kikithegecko/master_thesis/documentation/slides final/01.JPG

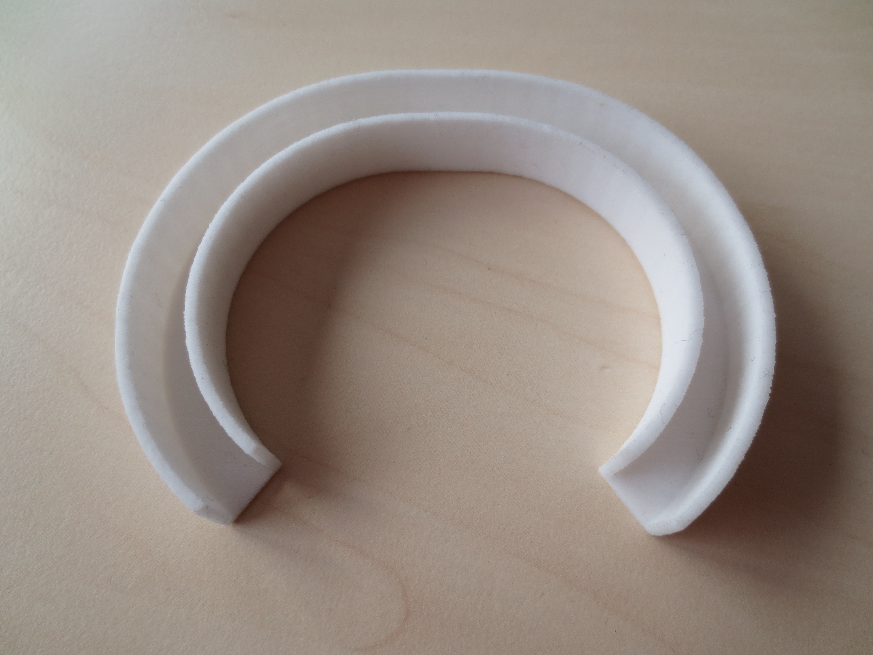
documentation/slides final/01.JPG
