kikithegecko/master_thesis/documentation/slides final/02.JPG

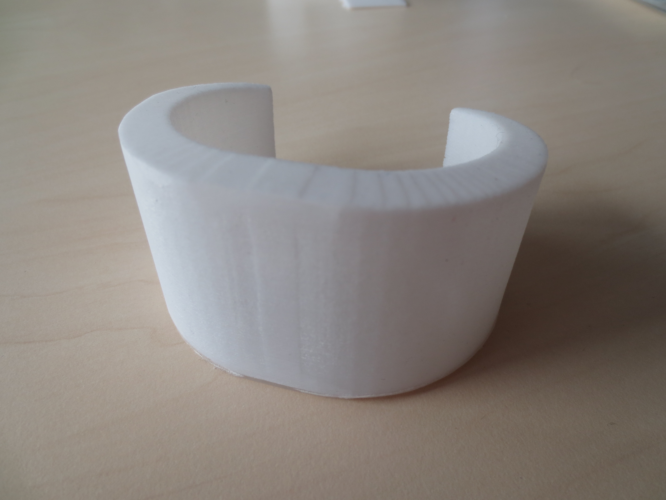
documentation/slides final/02.JPG
