kikithegecko/master_thesis/documentation/slides final/03.JPG

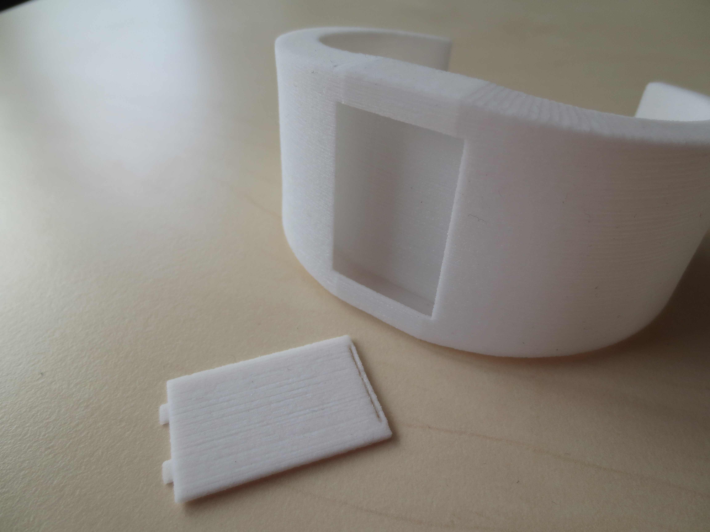
documentation/slides final/03.JPG
