kikithegecko/master_thesis/documentation/slides final/04.jpg

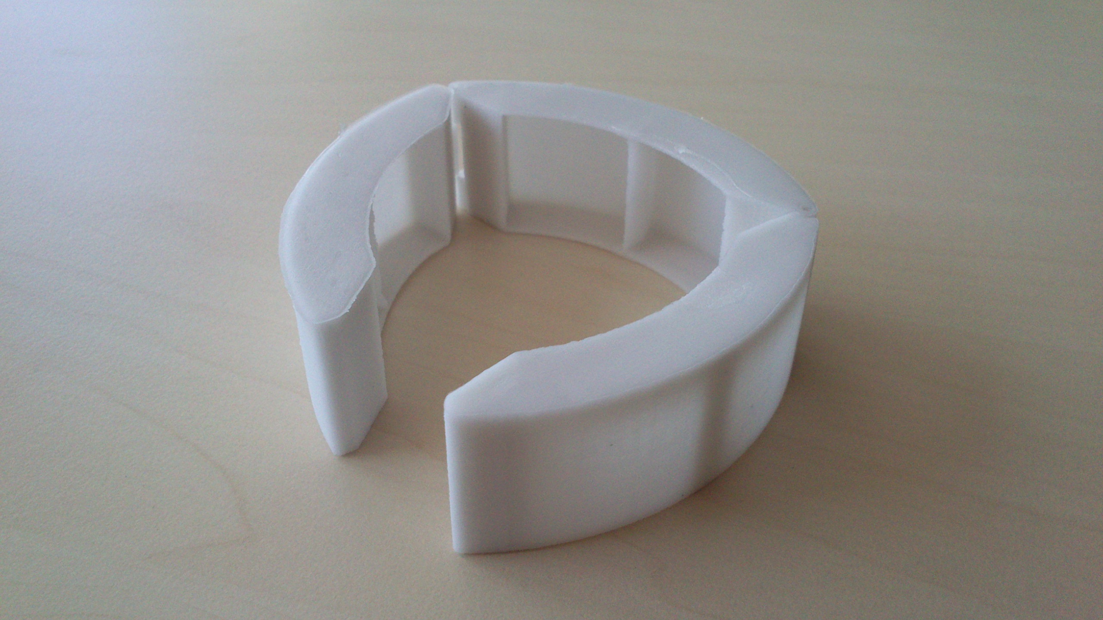
documentation/slides final/04.jpg
