kikithegecko/master_thesis/documentation/slides final/05.JPG

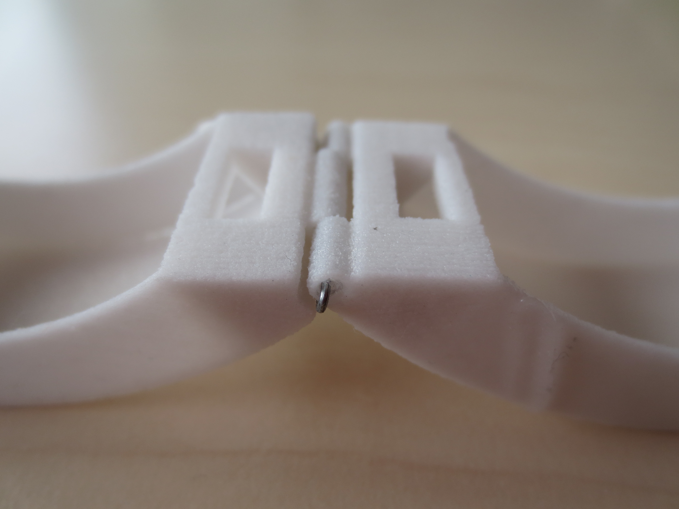
documentation/slides final/05.JPG
