kikithegecko/master_thesis/documentation/slides final/07.JPG

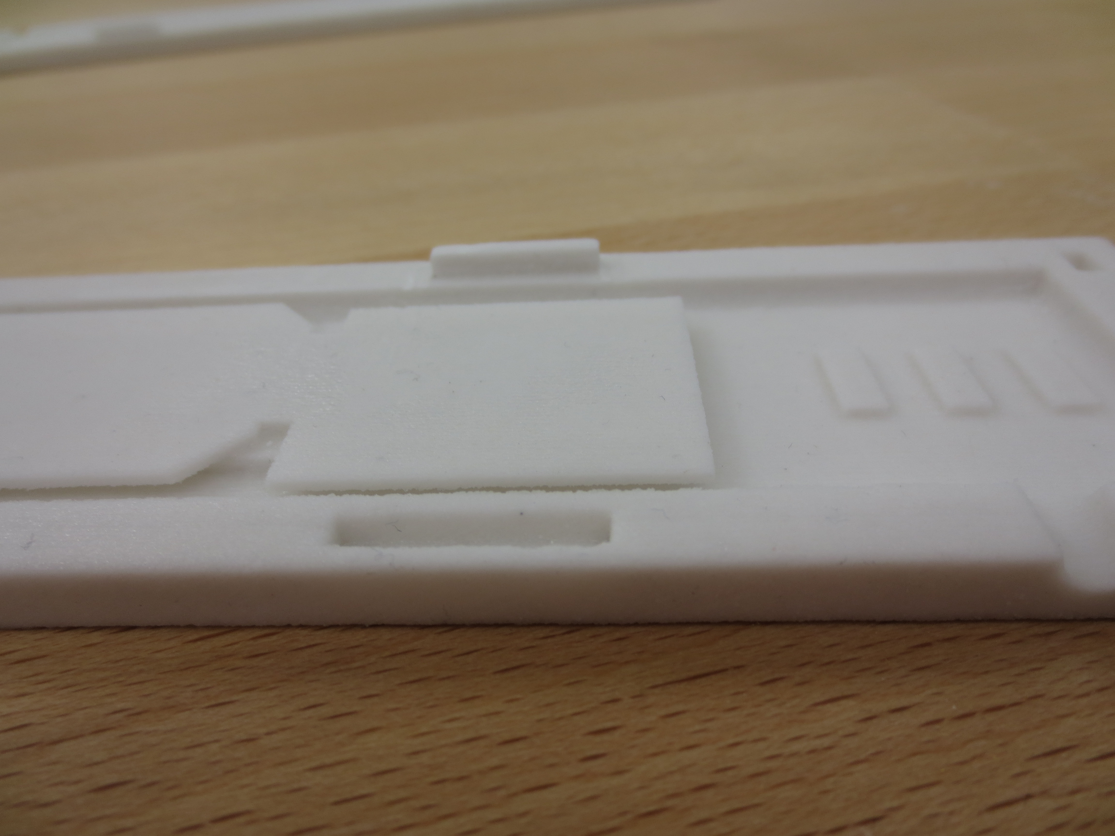
documentation/slides final/07.JPG
