kikithegecko/master_thesis/documentation/slides final/08.JPG

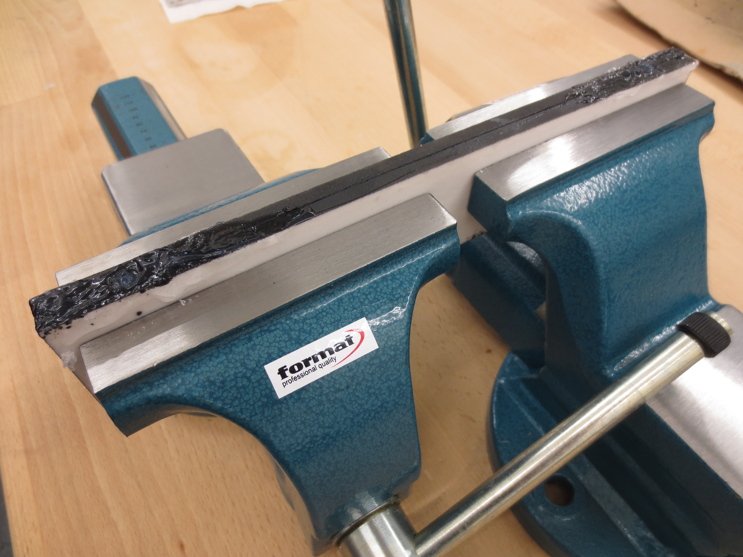
documentation/slides final/08.JPG
