kikithegecko/master_thesis/documentation/slides final/10.JPG

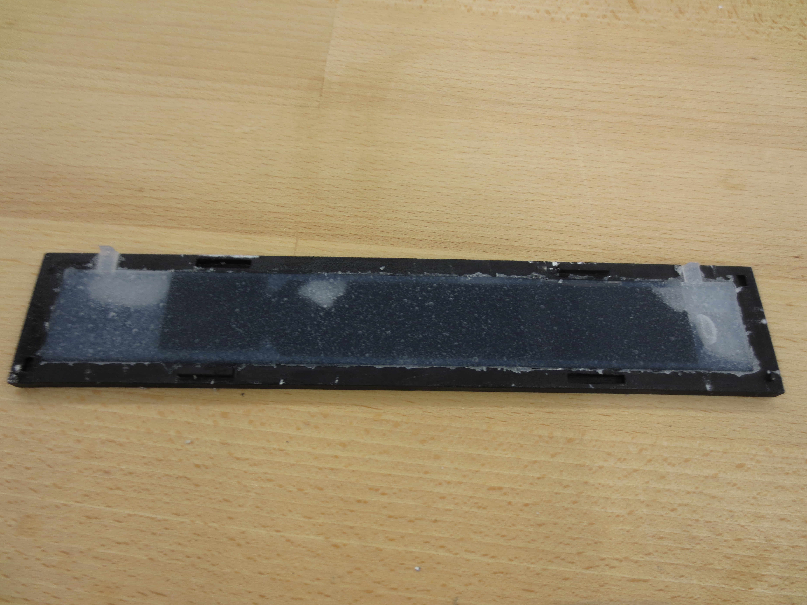
documentation/slides final/10.JPG
