kikithegecko/master_thesis/documentation/slides final/13.JPG

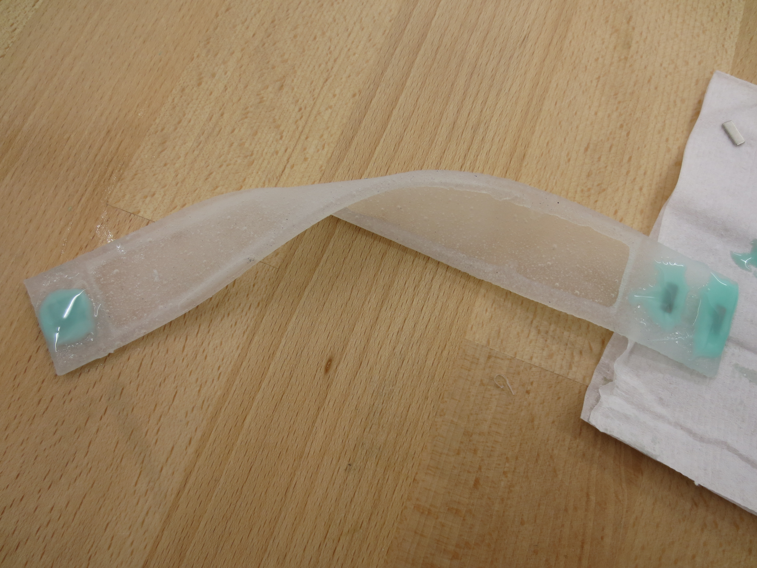
documentation/slides final/13.JPG
