kikithegecko/master_thesis/documentation/slides final/14.JPG

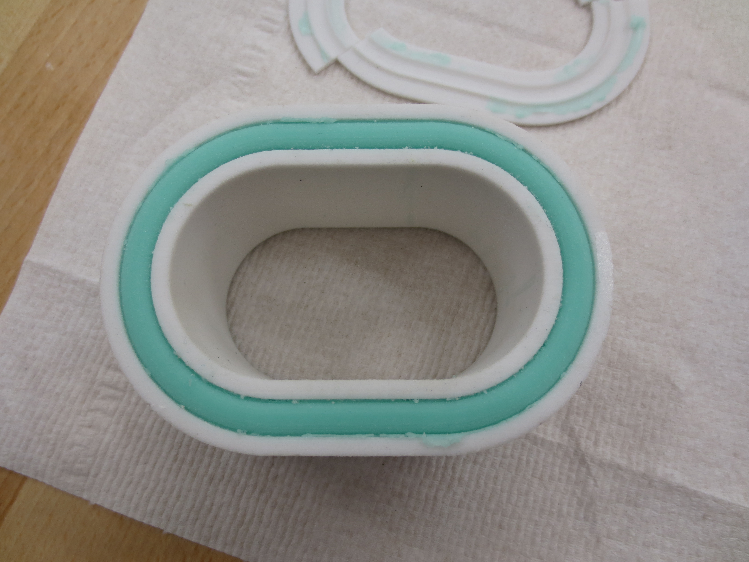
documentation/slides final/14.JPG
