kikithegecko/master_thesis/documentation/slides final/15.JPG

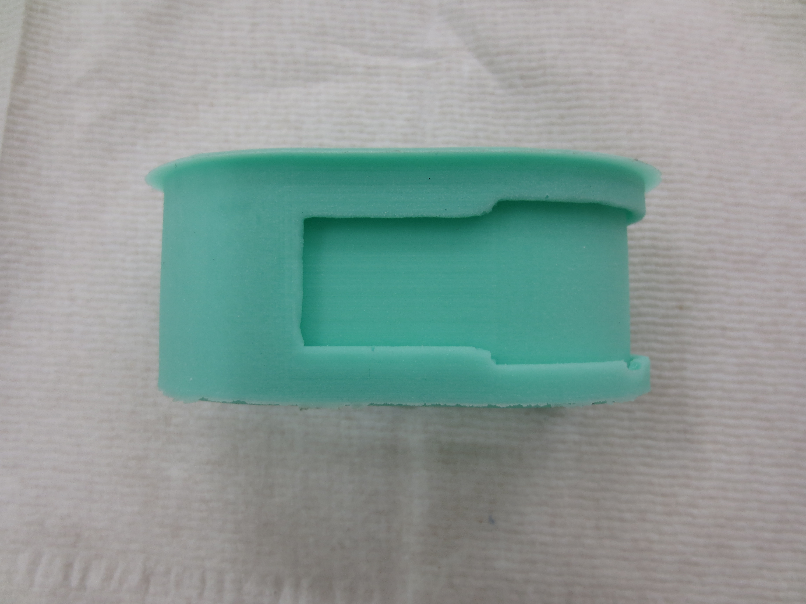
documentation/slides final/15.JPG
