kikithegecko/master_thesis/documentation/slides final/16.JPG

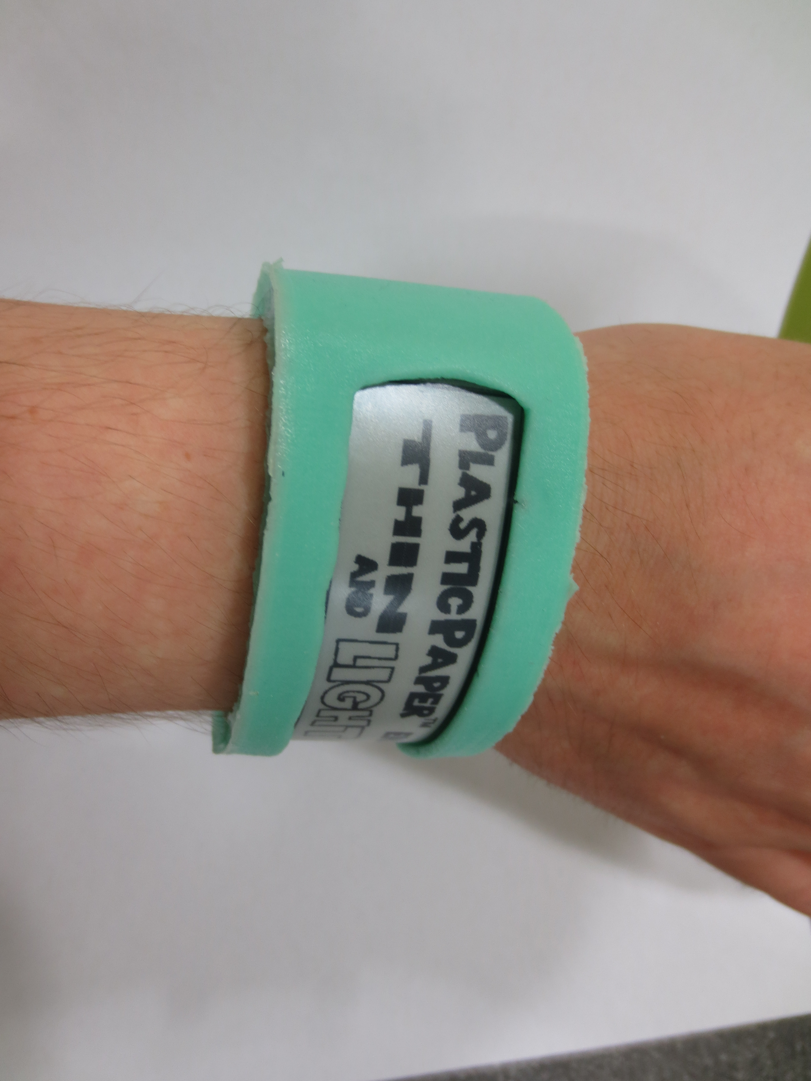
documentation/slides final/16.JPG
