kikithegecko/master_thesis/documentation/slides final/17.JPG

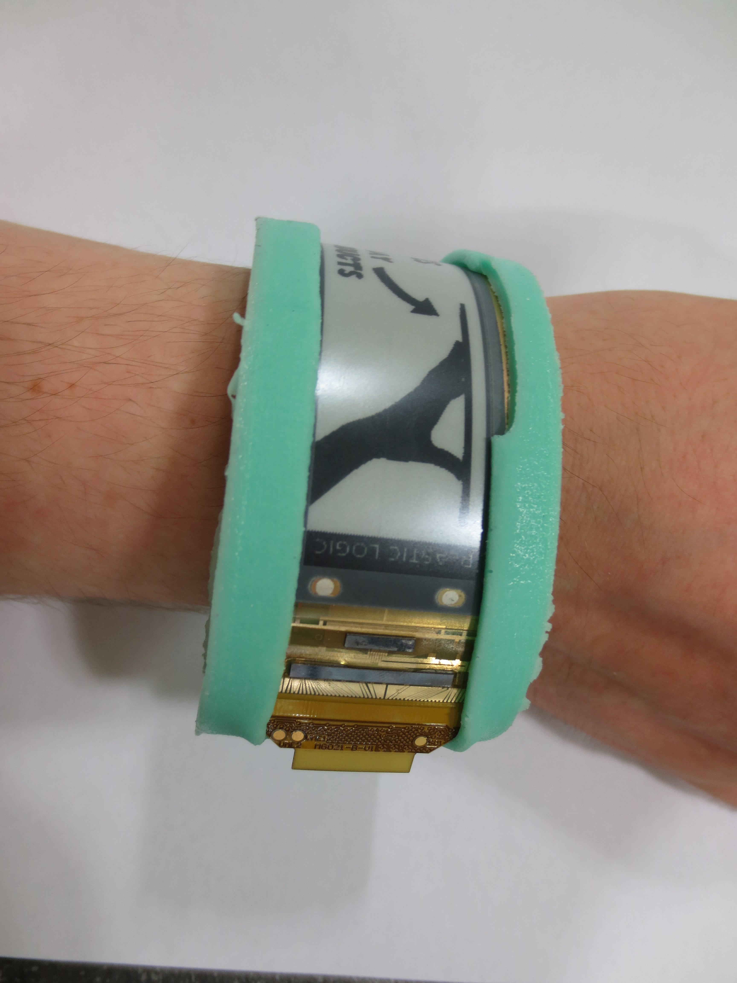
documentation/slides final/17.JPG
