kikithegecko/master_thesis/documentation/slides kick-off/finished.png

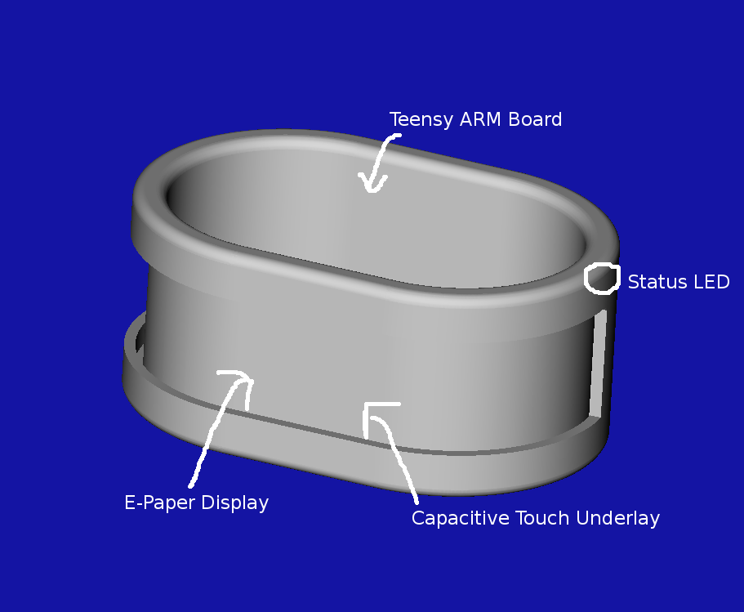
documentation/slides kick-off/finished.png
