kikithegecko/master_thesis/documentation/slides kick-off/IMG_0398.JPG

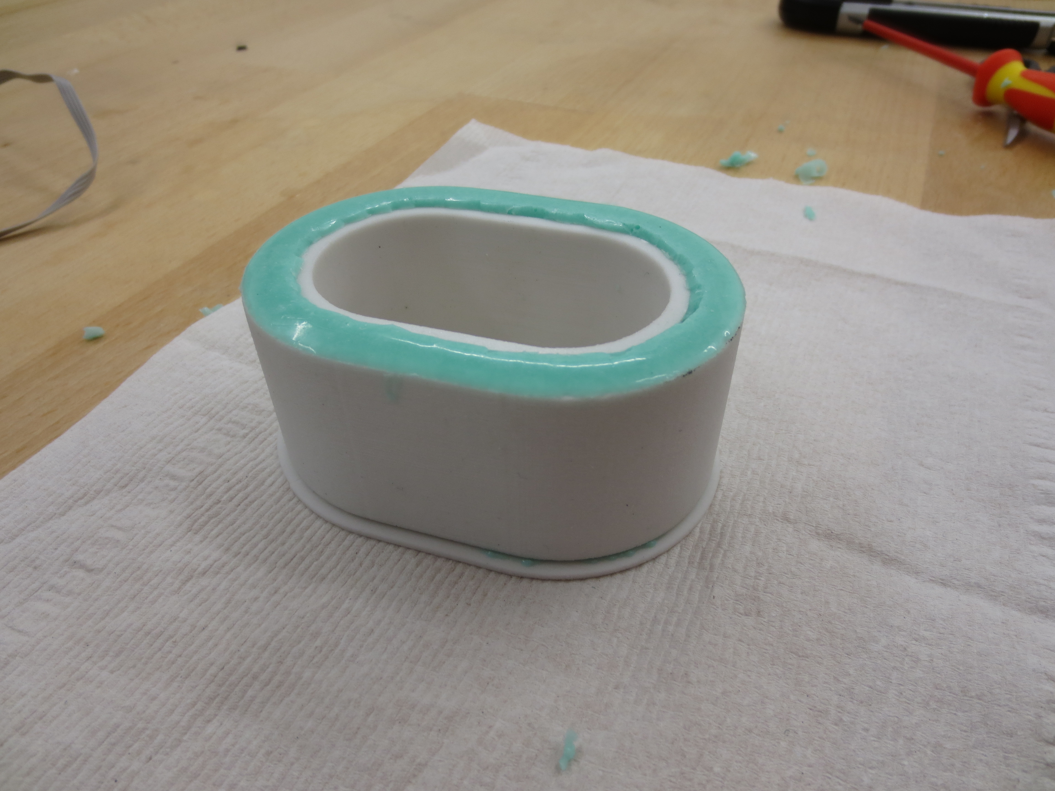
documentation/slides kick-off/IMG_0398.JPG
