kikithegecko/master_thesis/documentation/slides kick-off/IMG_0413.JPG

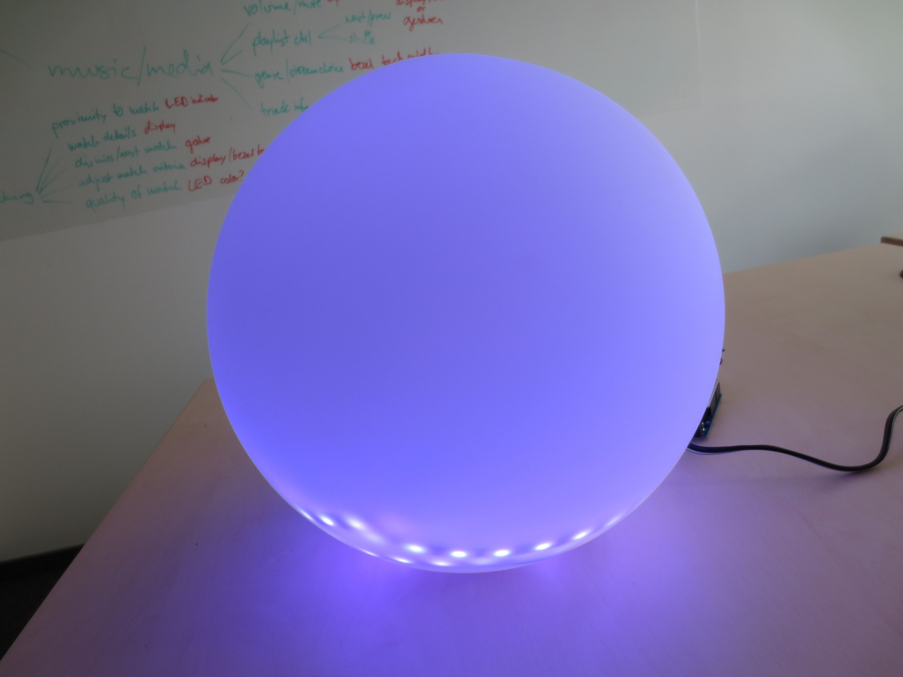
documentation/slides kick-off/IMG_0413.JPG
