kikithegecko/master_thesis/documentation/slides kick-off/IMG_0414.JPG

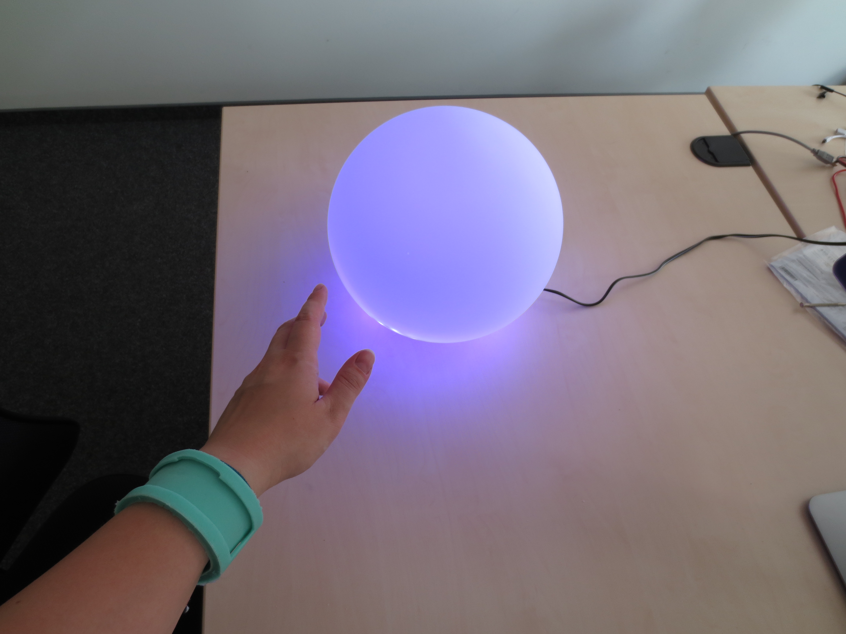
documentation/slides kick-off/IMG_0414.JPG
