kikithegecko/master_thesis/documentation/slides kick-off/IMG_0415.JPG

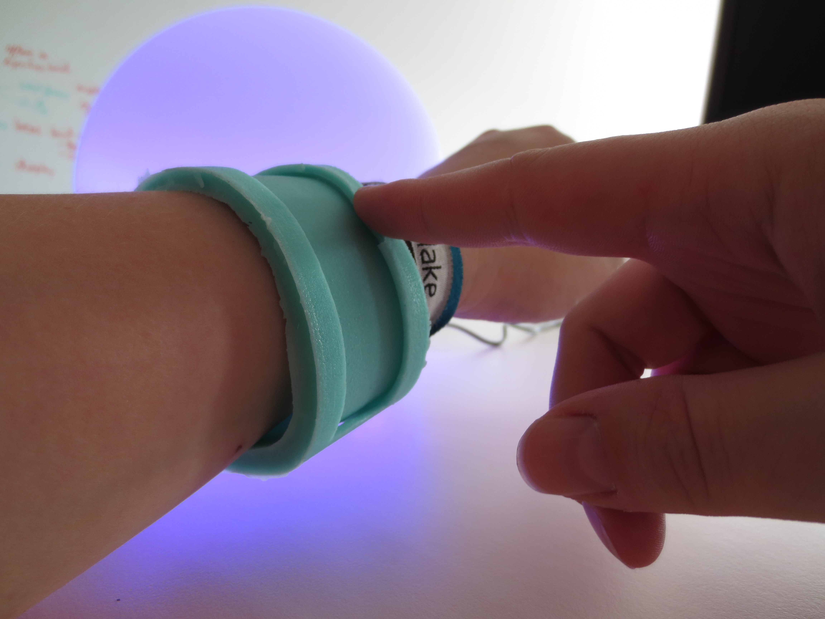
documentation/slides kick-off/IMG_0415.JPG
