kikithegecko/master_thesis/documentation/slides kick-off/IMG_0416.JPG

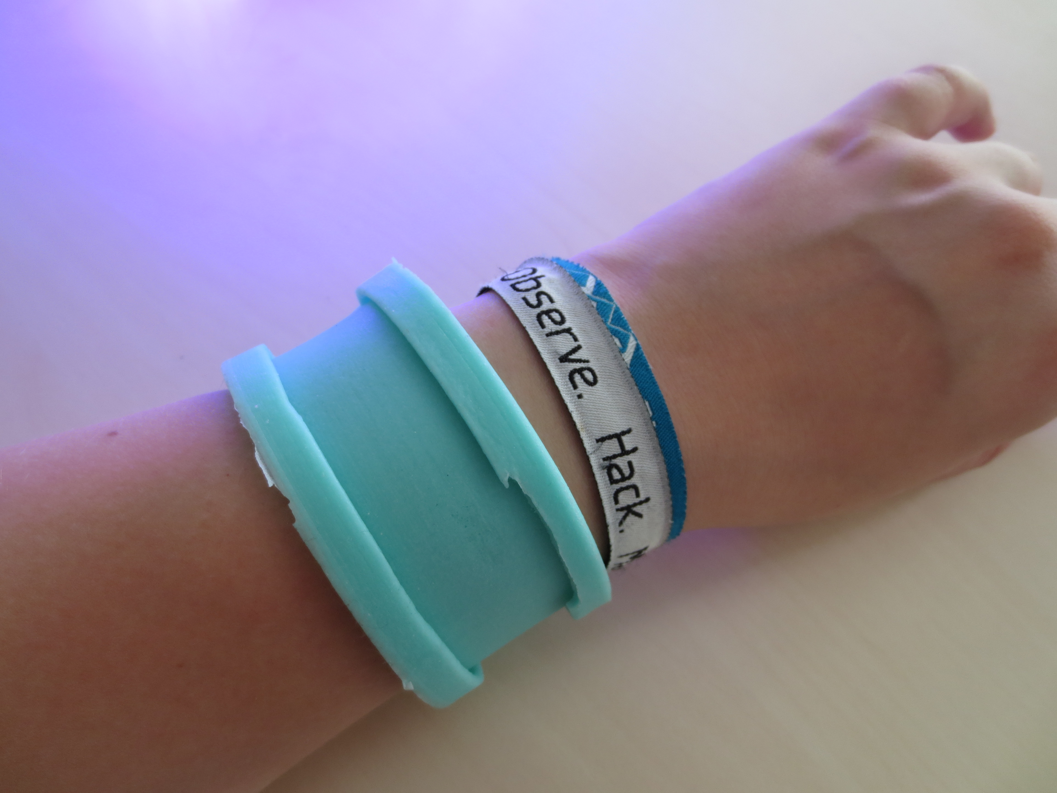
documentation/slides kick-off/IMG_0416.JPG
