kikithegecko/master_thesis/prints/06_mold2_inner.FCStd

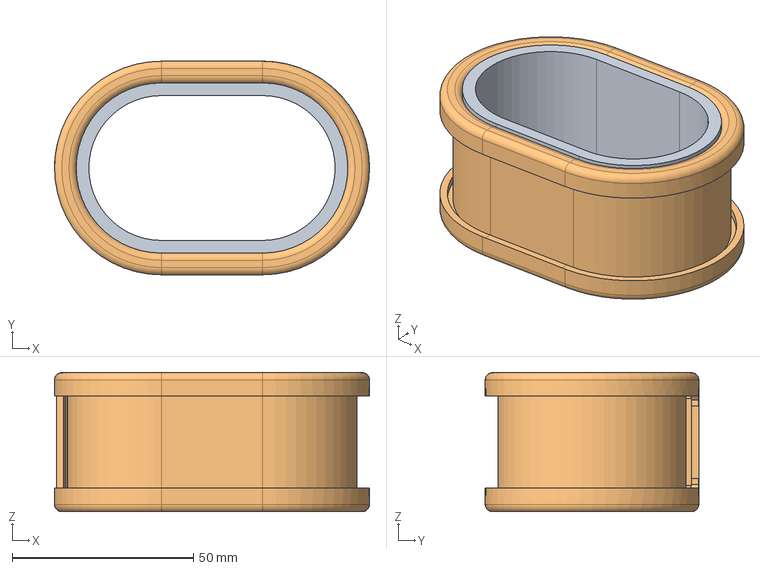
[picture p83: CAD file, 2014-07-16]
prints/06_mold2_inner.FCStd
87.0 x 59.0 x 38.5 mm
inner
