kikithegecko/master_thesis/prints/06_mold2.FCStd

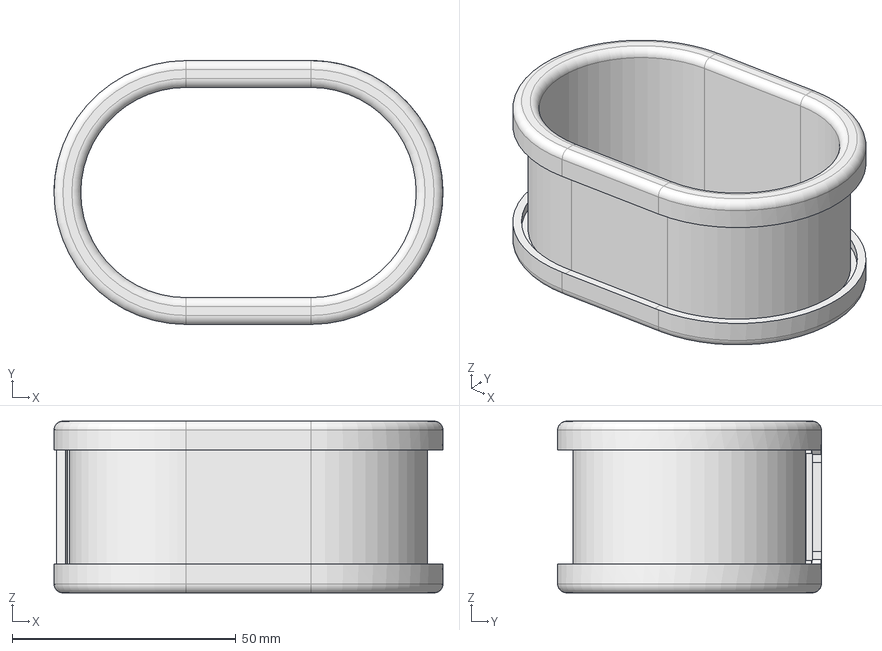
[picture p84: CAD file, 2014-07-16]
prints/06_mold2.FCStd
87.0 x 59.0 x 38.4 mm
