kikithegecko/master_thesis/prints/06_mold2_base.FCStd

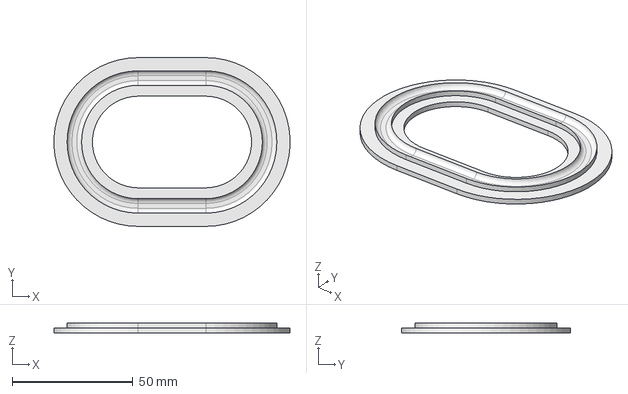
[picture p85: CAD file, 2014-07-16]
prints/06_mold2_base.FCStd
97.9 x 70.0 x 4.00 mm
