kikithegecko/master_thesis/prints/06_mold2_outer.FCStd

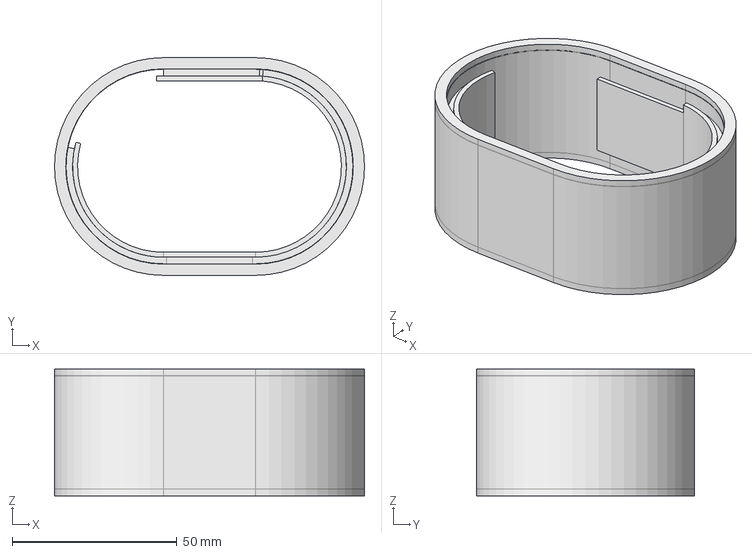
[picture p86: CAD file, 2014-07-16]
prints/06_mold2_outer.FCStd
94.0 x 66.0 x 38.4 mm
