kikithegecko/master_thesis/prints/06_mold2_finished_product.FCStd

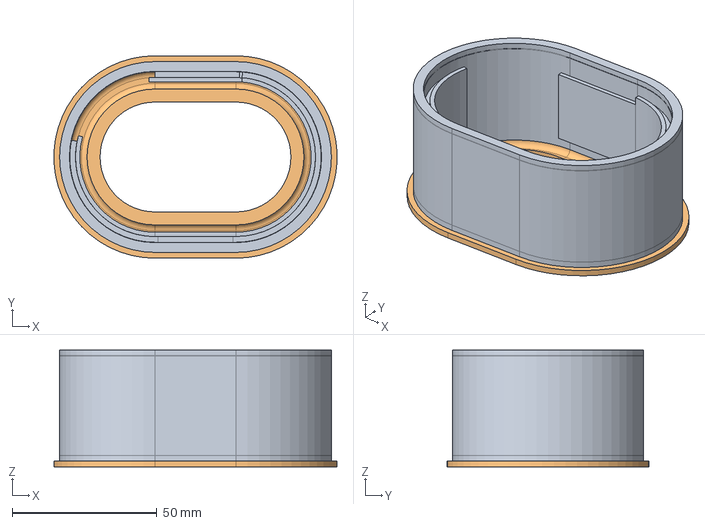
[picture p87: CAD file, 2014-07-16]
prints/06_mold2_finished_product.FCStd
97.9 x 70.0 x 40.4 mm
outer
base
