kikithegecko/master_thesis/prints/05_silicone_bracelet_moldable.FCStd

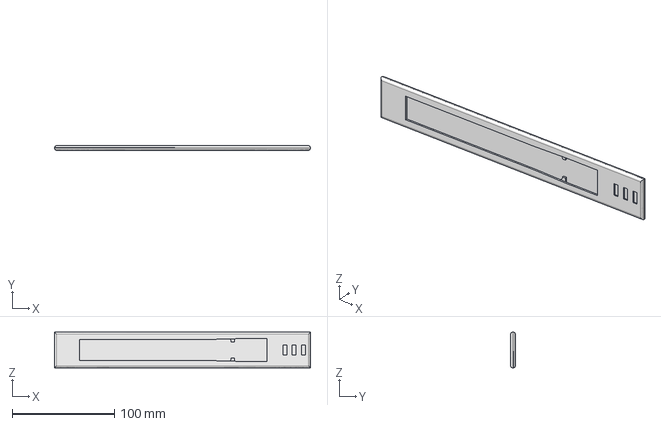
[picture p88: CAD file, 2014-07-10]
prints/05_silicone_bracelet_moldable.FCStd
250.0 x 4.50 x 35.0 mm
