kikithegecko/master_thesis/prints/05_silicone_bracelet_mold.FCStd

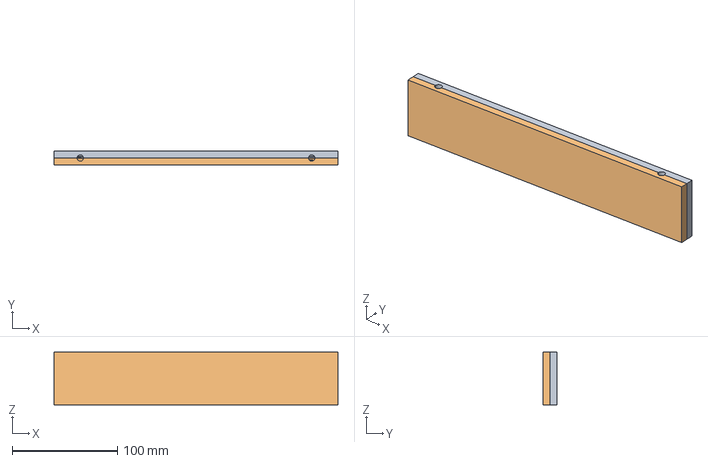
[picture p89: CAD file, 2014-07-10]
prints/05_silicone_bracelet_mold.FCStd
270.0 x 13.0 x 50.0 mm
