kikithegecko/master_thesis/prints/02a_confortable_cuff_improved.FCStd

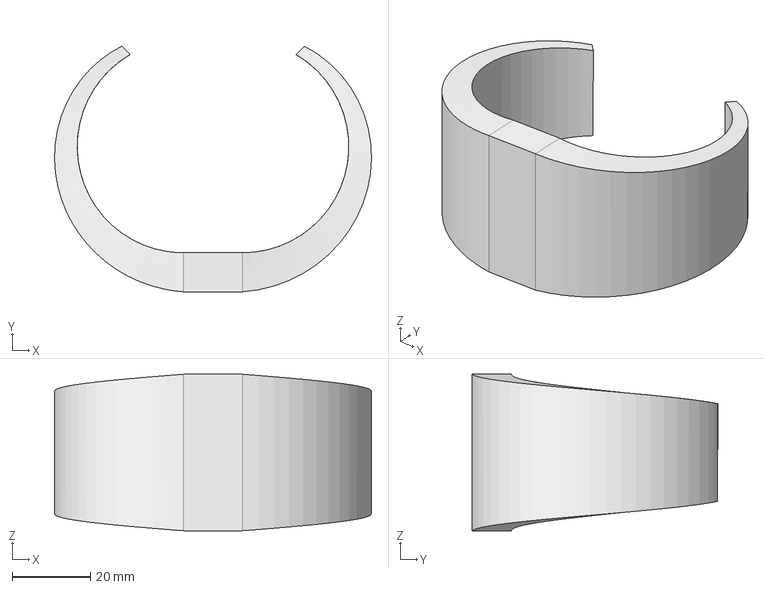
[picture p90: CAD file, 2014-06-16]
prints/02a_confortable_cuff_improved.FCStd
81.0 x 62.8 x 40.0 mm
