kikithegecko/master_thesis/prints/02a_lid.FCStd

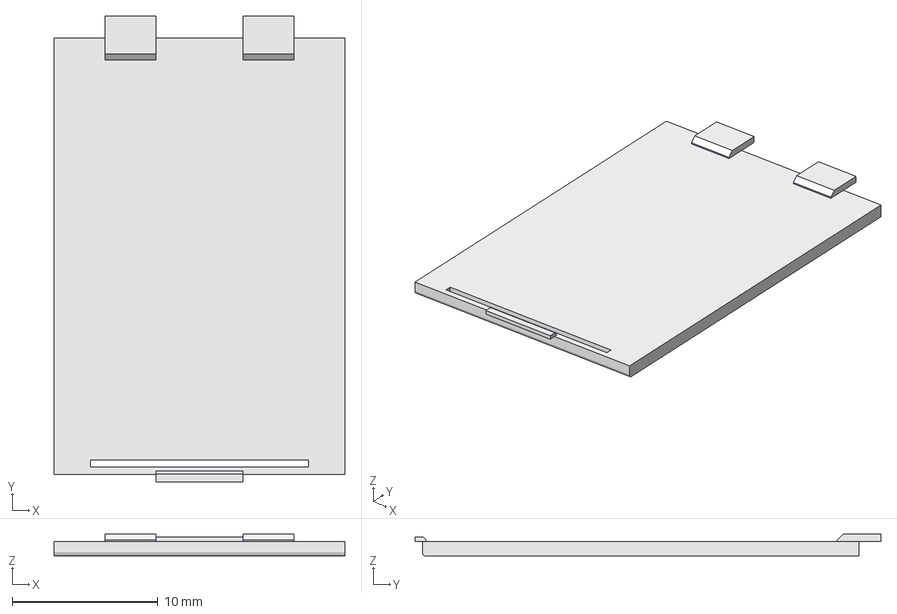
[picture p91: CAD file, 2014-06-16]
prints/02a_lid.FCStd
20.0 x 32.0 x 1.50 mm
