kikithegecko/master_thesis/prints/04b_tri_part_end.FCStd

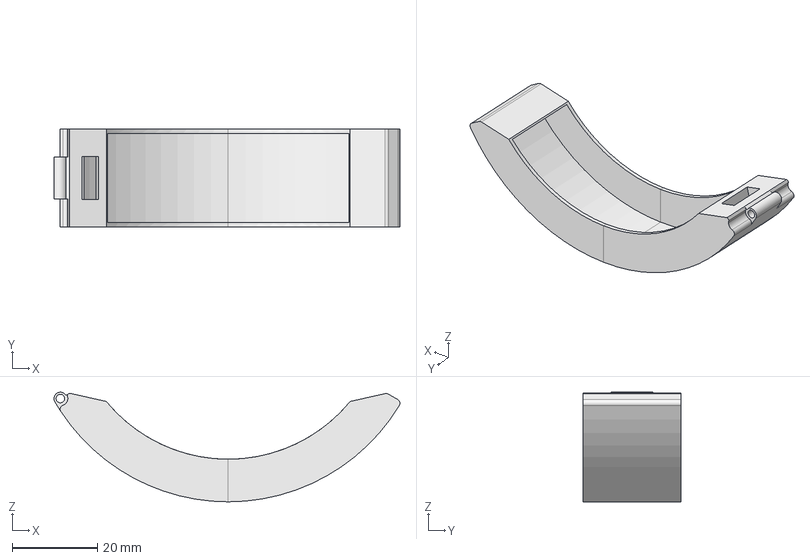
[picture p92: CAD file, 2014-05-23]
prints/04b_tri_part_end.FCStd
81.2 x 23.0 x 25.7 mm
