kikithegecko/master_thesis/prints/04b_tri_part_middle.FCStd

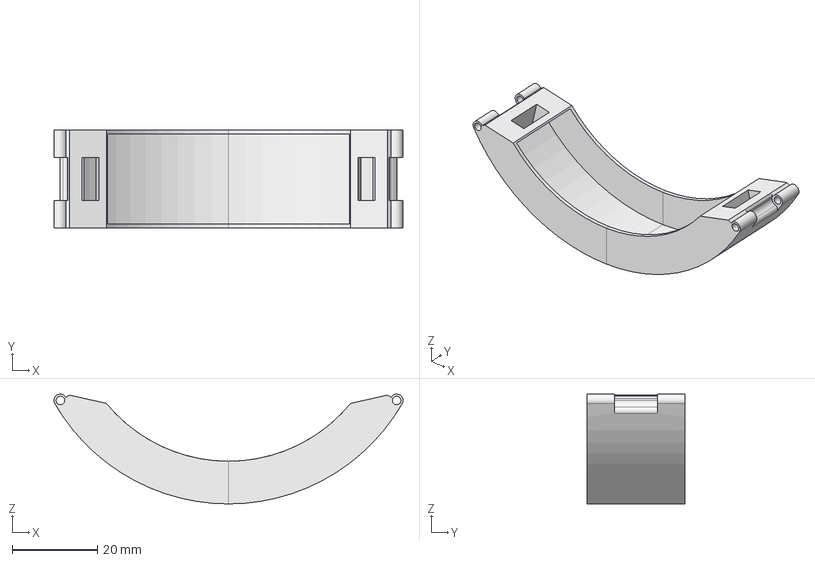
[picture p93: CAD file, 2014-05-23]
prints/04b_tri_part_middle.FCStd
81.8 x 23.0 x 25.7 mm
