kikithegecko/master_thesis/prints/04a_tri_part_middle.FCStd

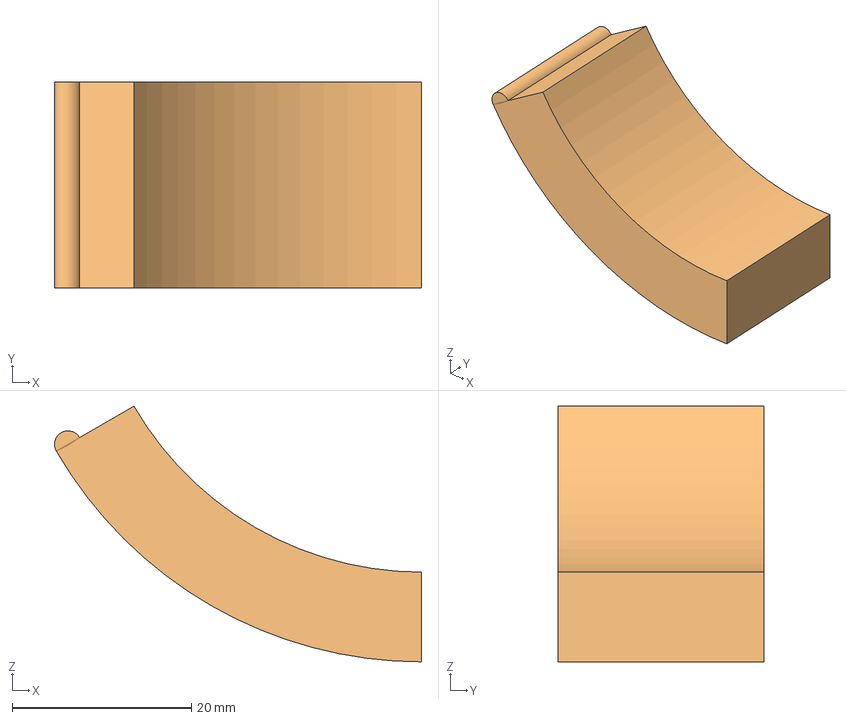
[picture p94: CAD file, 2014-05-23]
prints/04a_tri_part_middle.FCStd
40.9 x 23.0 x 28.5 mm
hinge cut
hinge pad
Sweep profile
