kikithegecko/master_thesis/prints/04_tri_part_end.FCStd

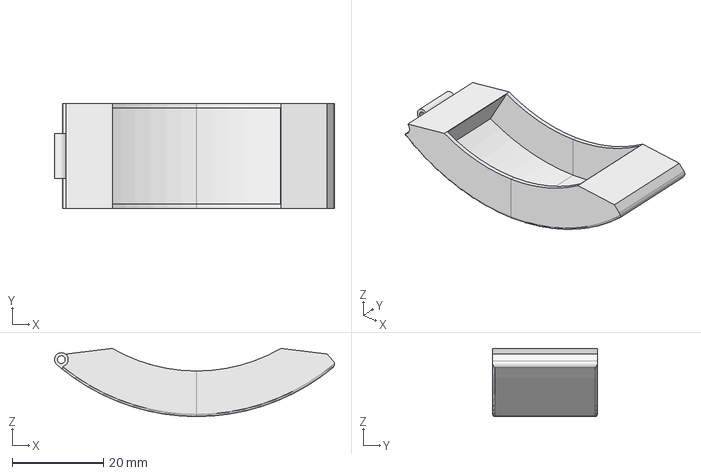
[picture p95: CAD file, 2014-05-20]
prints/04_tri_part_end.FCStd
61.4 x 23.0 x 15.0 mm
