kikithegecko/master_thesis/prints/04_tri_part_middle.FCStd

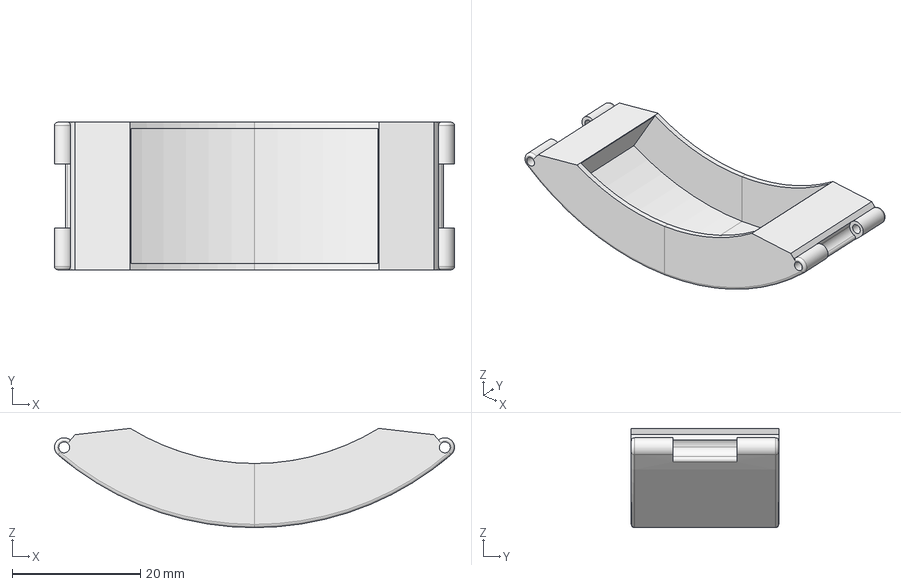
[picture p96: CAD file, 2014-05-20]
prints/04_tri_part_middle.FCStd
62.4 x 23.0 x 15.5 mm
