kikithegecko/master_thesis/prints/03_amico_side.stl

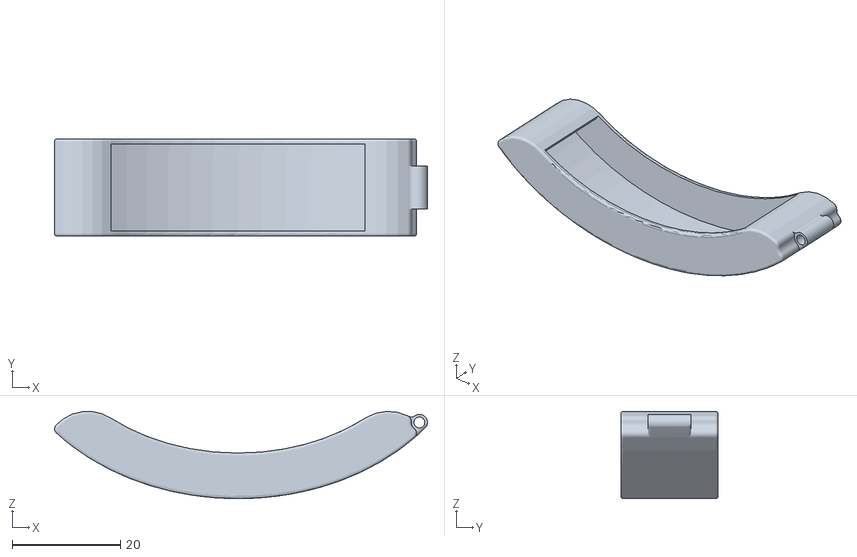
[picture p97: CAD file, 2014-05-20]
prints/03_amico_side.stl
68.9 x 18.0 x 16.1
