kikithegecko/master_thesis/prints/03_amico_bracelet.stl

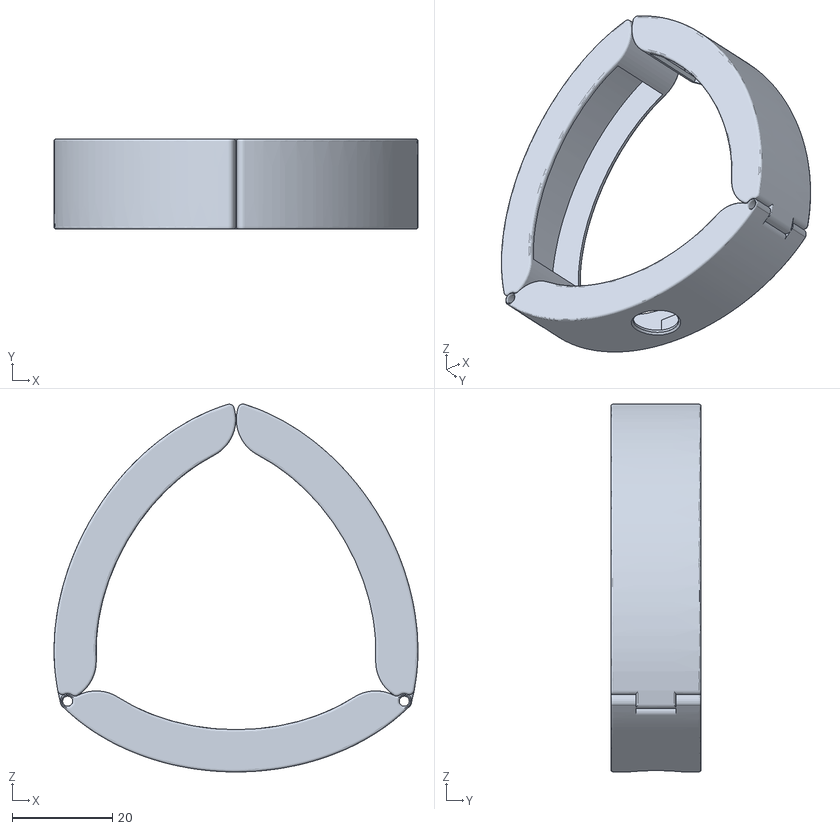
[picture p98: CAD file, 2014-05-20]
prints/03_amico_bracelet.stl
72.4 x 18.0 x 73.2
