kikithegecko/master_thesis/prints/03_amico_front.stl

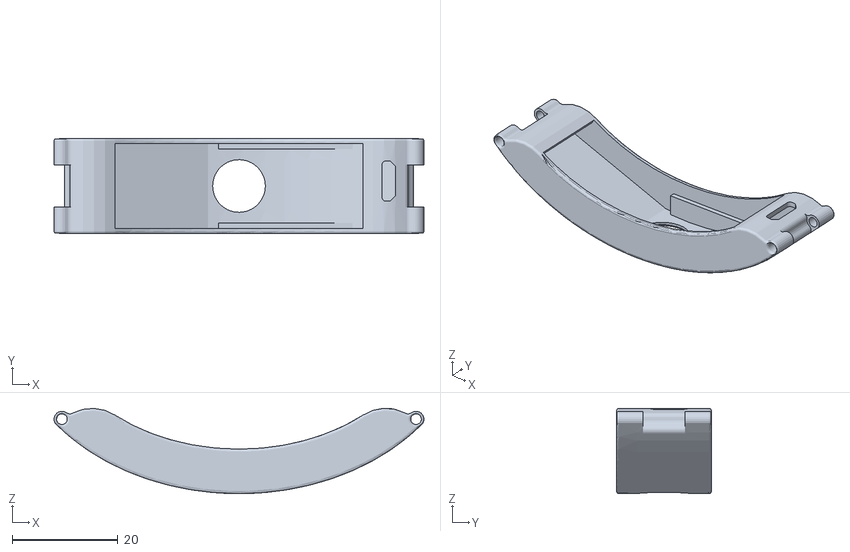
[picture p99: CAD file, 2014-05-20]
prints/03_amico_front.stl
70.0 x 18.0 x 16.1
