kikithegecko/master_thesis/prints/02_comfortable_cuff.FCStd

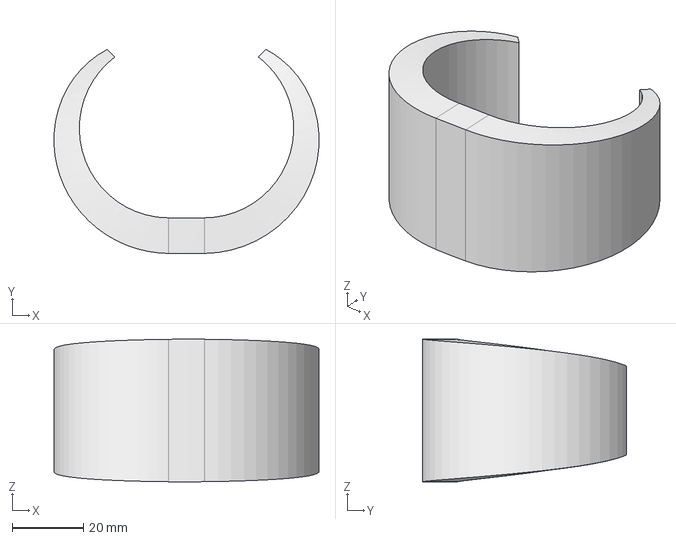
[picture p100: CAD file, 2014-05-20]
prints/02_comfortable_cuff.FCStd
74.4 x 57.3 x 40.1 mm
