kikithegecko/master_thesis/prints/01_simple_cuff.FCStd

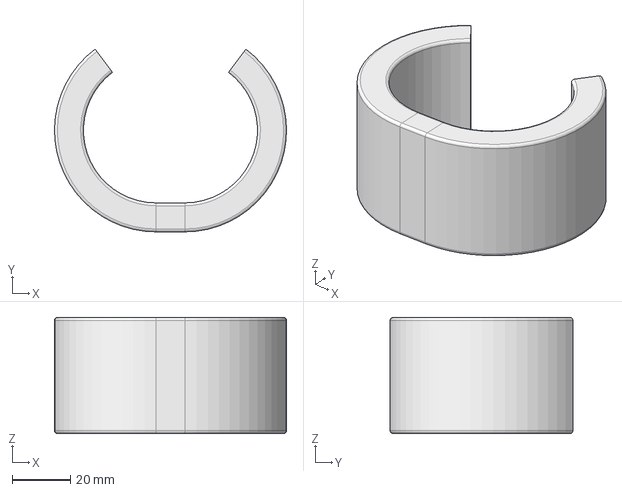
[picture p101: CAD file, 2014-05-20]
prints/01_simple_cuff.FCStd
80.0 x 63.0 x 40.0 mm
