kikithegecko/master_thesis/prints/01_simple_cuff_no_fillets.stl

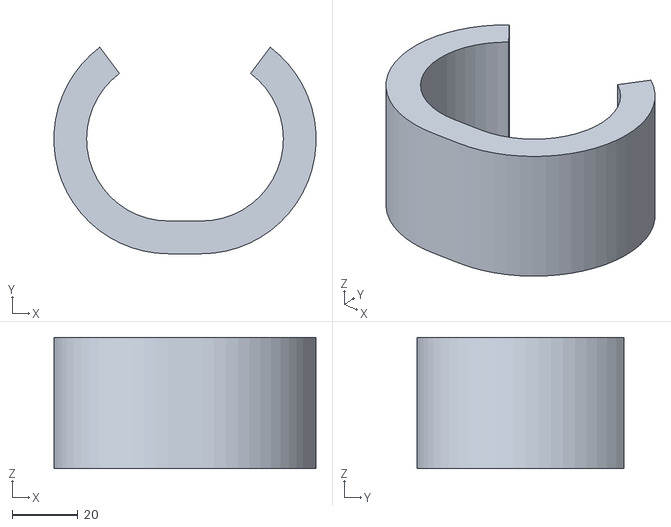
[picture p102: CAD file, 2014-05-20]
prints/01_simple_cuff_no_fillets.stl
79.9 x 63.0 x 40.0
