kikithegecko/master_thesis/code/bracelet/gesture_recognizer/datawrangler.py

import serial

s = serial.Serial('/dev/ttyACM0', 115200)
filename = 80

while True:
	line = s.readline().decode('ascii')
	if line == "start recording\r\n":
		f = open(str(filename)+".txt", "w")
		for i in range(150): #current sample size is 150
			gesture = []
			line = s.readline().decode('ascii')
			line = line.replace('\r', '')
			f.write(line)
		f.close()
		print("File #" + str(filename) + " saved.")
		filename += 1
