kikithegecko/master_thesis/code/lamp/lamp_shield_test/lamp_shield_test.ino

#include <SoftwareSerial.h>

#define rxPin 2
#define txPin 4

#define RPin 5
#define GPin 3
#define BPin 6

int red = 0;
int green = 0;
int blue = 125;

int newRed, newGreen, newBlue;

String inputString = ""; // for incoming data
boolean stringComplete = false;

SoftwareSerial bluetooth(rxPin, txPin);

void setup() {
  pinMode(RPin, OUTPUT);
  pinMode(GPin, OUTPUT);
  pinMode(BPin, OUTPUT);
  
  Serial.begin(9600);
 Serial.println("Serial ready");
  
  //taken from https://wiki.hci.uni-hannover.de/doku.php?id=research:thesis:ems-navigation:prototyping
  bluetooth.begin(115200);        // The Bluetooth Mate defaults to 115200bps
  delay(320);                     // IMPORTANT DELAY! (Minimum ~276ms)
  bluetooth.print("$$$");         // Enter command mode
  delay(15);                      // IMPORTANT DELAY! (Minimum ~10ms)
  bluetooth.println("U,9600,N");  // Temporarily Change the baudrate to 9600, no parity
  bluetooth.begin(9600);          // Start bluetooth serial at 9600
  
  bluetooth.println("Bluetooth ready");
}

void fade(int newR, int newG, int newB){
  int stepR, stepG, stepB;

  while(red != newR || green != newG || blue != newB){
    if(newR > red){
      red++;}
    else if(newR < red){
      red--;}
    if(newG > green)
      green++;
    else if(newG < green){
      green--;}
    if(newB > blue){
      blue++;}
    else if(newB < blue){
      blue--;}
    
    analogWrite(RPin, red);
    analogWrite(GPin, green);
    analogWrite(BPin, blue);
    //delay(10);
  }

  red = newR;
  green = newG;
  blue = newB;
}

void loop() {
  
  if(stringComplete) {
    // protocol is "rrrgggbbb", so check length and syntax
    if(inputString.length() != 10){
        bluetooth.println("Error! Wrong String length!");
    }
    else { // decompose and convert      
      newRed = (String(inputString[0]) + String(inputString[1]) + String(inputString[2])).toInt();
      newGreen = (String(inputString[3]) + String(inputString[4]) + String(inputString[5])).toInt();
      newBlue = (String(inputString[6]) + String(inputString[7]) + String(inputString[8])).toInt();
      
      fade(newRed, newGreen, newBlue);
      //red = newRed;
      //green = newGreen;
      //blue = newBlue;
      
      /*  
      Serial.print("R: ");
      Serial.print(red);
      Serial.print(" G: ");
      Serial.print(green);
      Serial.print(" B: ");
      Serial.println(blue);
      */
    }
    inputString = "";
    stringComplete = false;
  }
  
  analogWrite(RPin, red);
  analogWrite(GPin, green);
  analogWrite(BPin, blue);
  
  if(bluetooth.available()) {
    char inChar = bluetooth.read();
    inputString += inChar;
    if(inChar == '\n') {
      stringComplete = true;
    }
  }
}
