kikithegecko/master_thesis/documentation/slides final/11.JPG

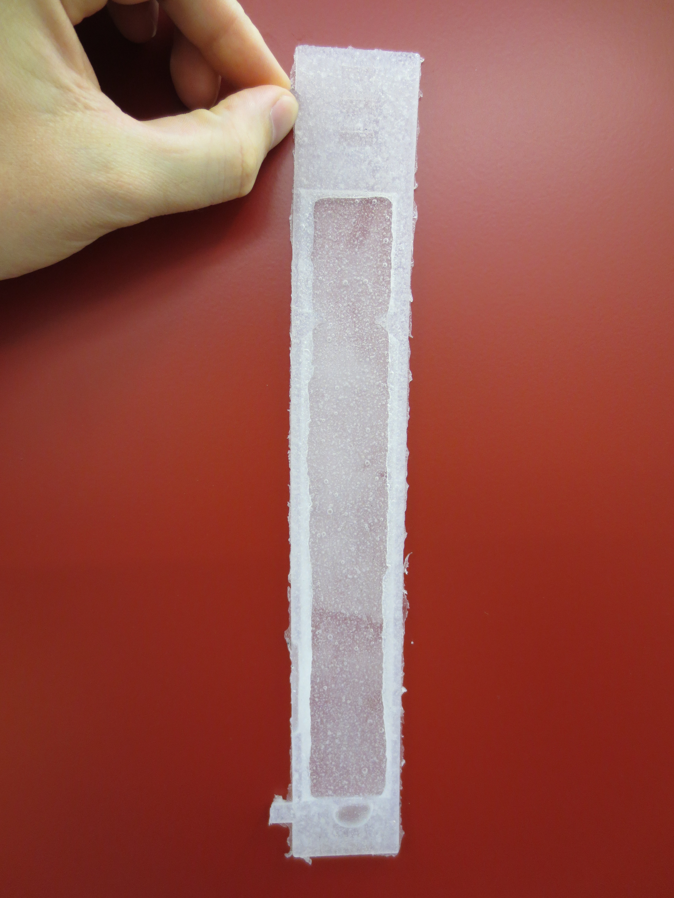
documentation/slides final/11.JPG
