kikithegecko/master_thesis/documentation/slides kick-off/IMG_0410.JPG

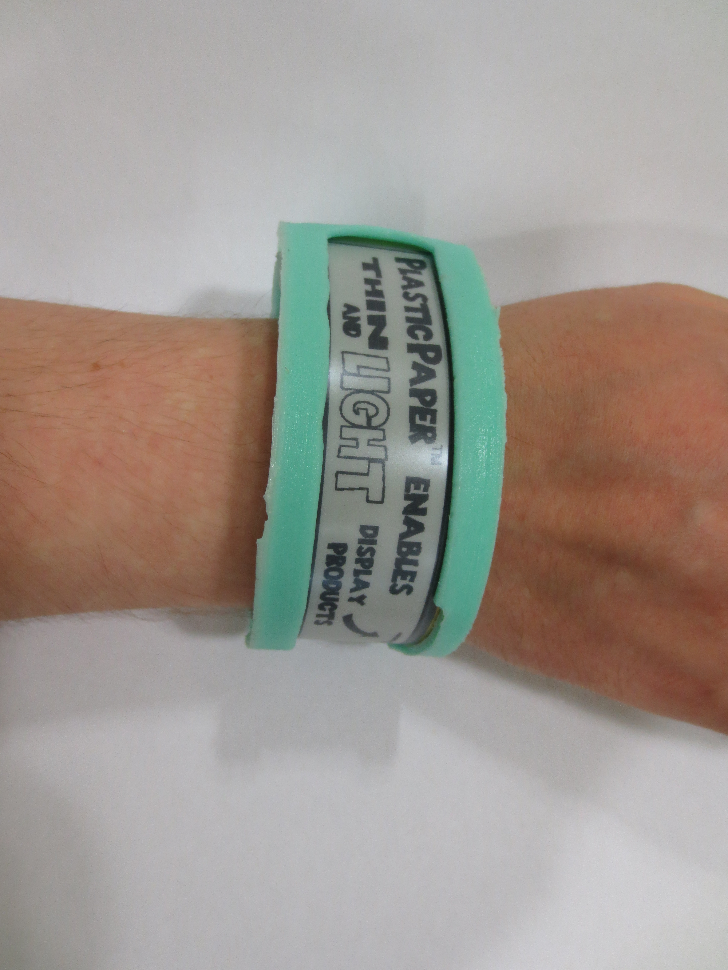
documentation/slides kick-off/IMG_0410.JPG
